simon-frankau/dumb-vga/data/cat.png

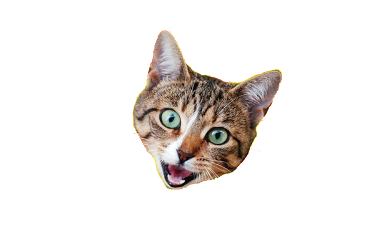
data/cat.png
